JoonatanAlanampa/cartridge_pmod/rb.png

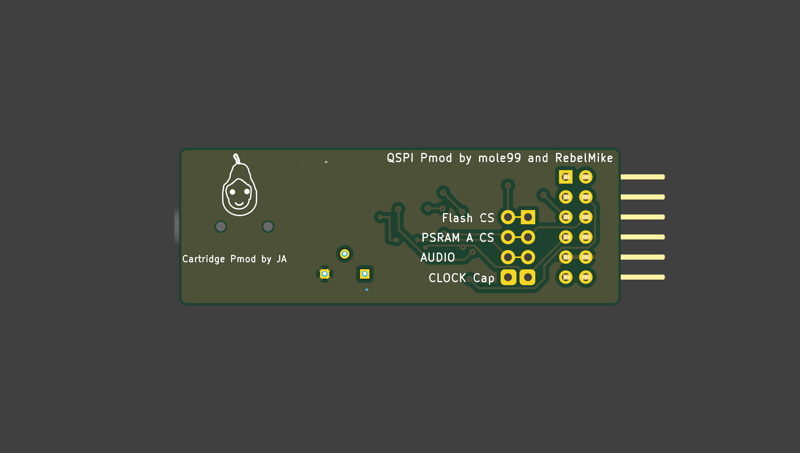
rb.png
