JoonatanAlanampa/cartridge_pmod/render_ext.png

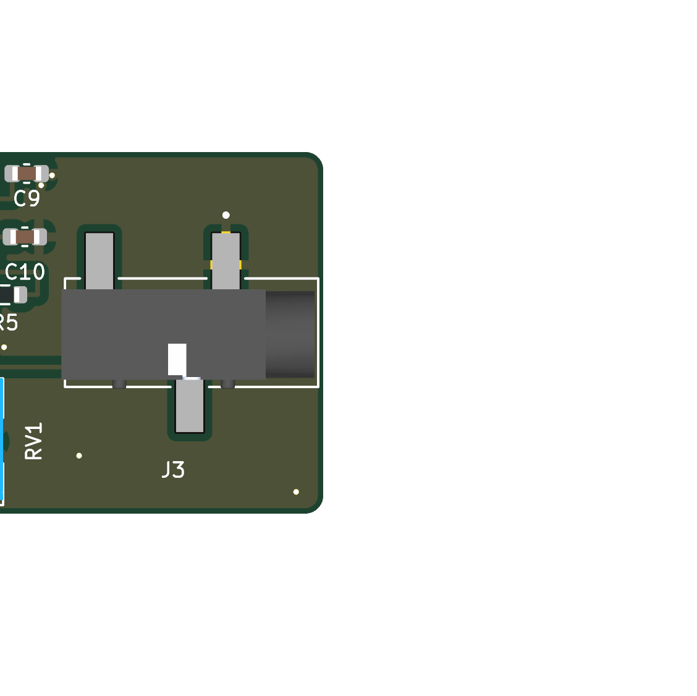
render_ext.png
