JoonatanAlanampa/cartridge_pmod/render_side_crop.png

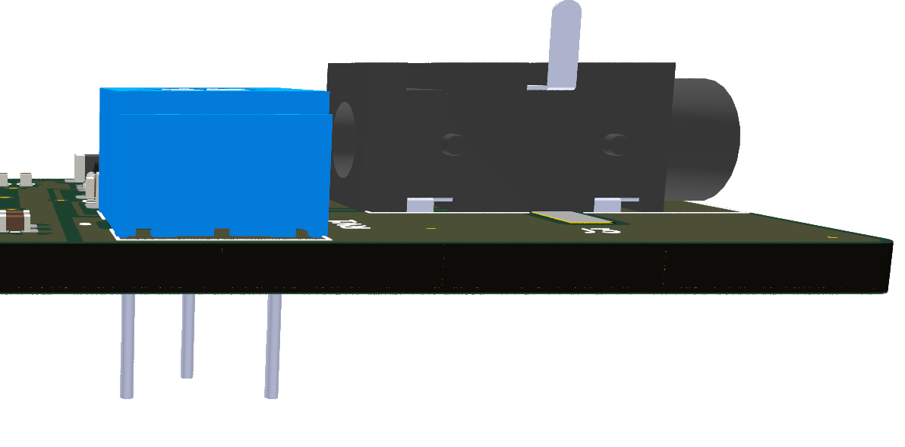
render_side_crop.png
