JoonatanAlanampa/cartridge_pmod/render_top.png

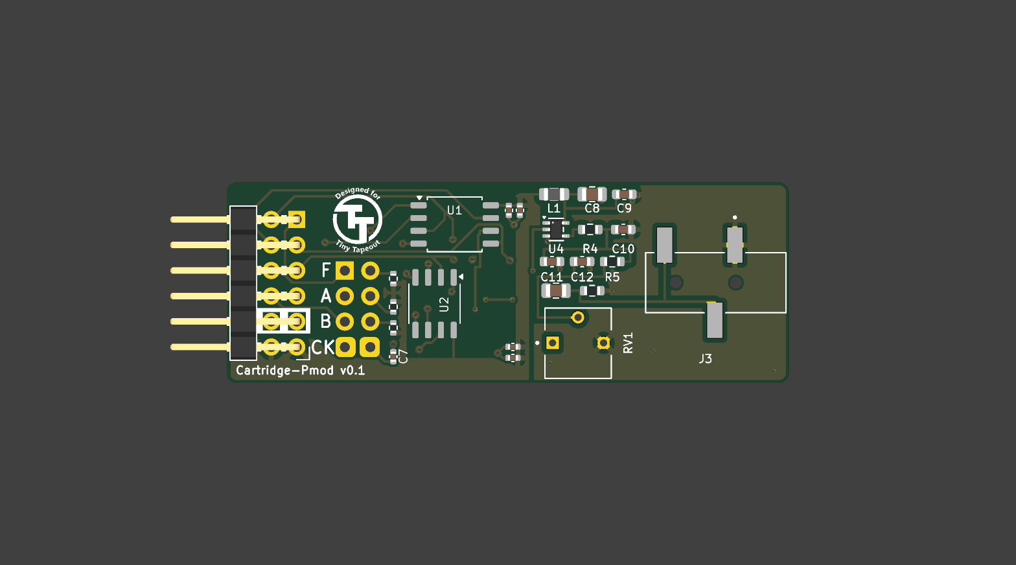
render_top.png
