JoonatanAlanampa/cartridge_pmod/rs_crop.png

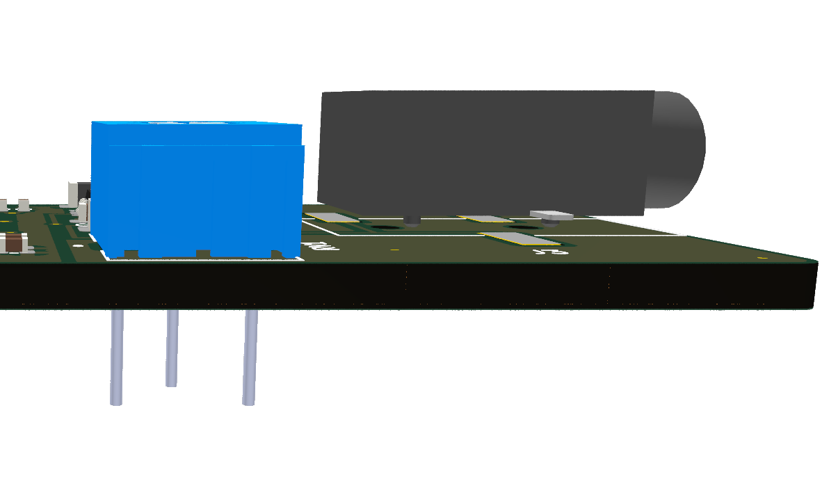
rs_crop.png
