JoonatanAlanampa/cartridge_pmod/rt_crop.png

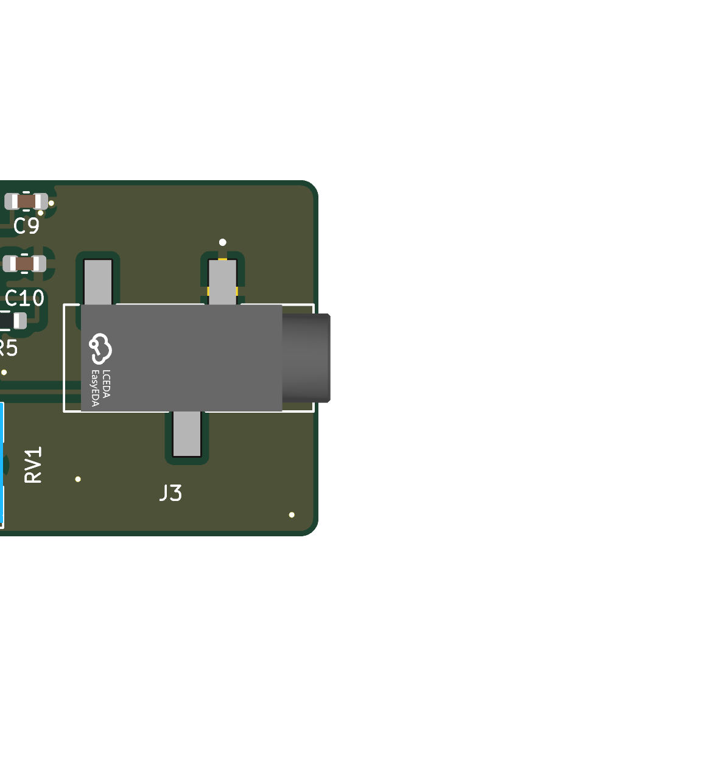
rt_crop.png
