JoonatanAlanampa/cartridge_pmod/tools/pearto_preview.png

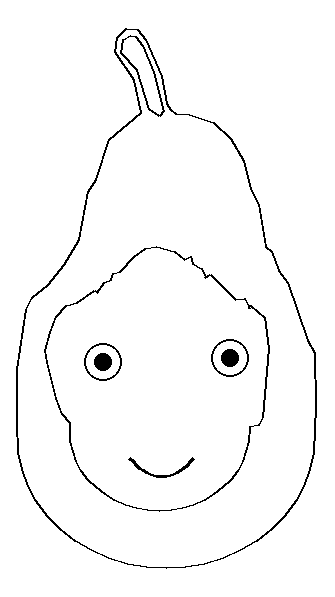
tools/pearto_preview.png
