JoonatanAlanampa/cartridge_pmod/refs/tt-audio-pmod/sim/ACSweep.asc

C1: cap; 100n
C2: cap; 47µ
C3: cap; 147n
R1: res; 33
R2: res; R={vol}
R3: res; 470
R4: res; 37R
R5: res; 17
R6: res; 120
V1: voltage; 1.6; AC 1.5 0
Named nets: out, 0
.param period=0.00001013/3
#.step param sweep list 0.001 0.0005 0.0002 0.0001 0.00005
.param sweep=0.001
.ac dec 20 1 1000000
#.step dec param vol 20 200 3
.param vol=180
