JoonatanAlanampa/cartridge_pmod/refs/tt-audio-pmod/sim/LineOutPWM.asc

B1: bv; V=3.3*((time/{period})-(int(time/{period}))<0.5+0.5*sin(2*pi*((time/{sweep})-(int(time/{sweep})))))
C1: cap; 100n
C2: cap; 47µ
C3: cap; 147n
R1: res; 33
R2: res; 33
R3: res; 470
R4: res; 37R
R5: res; 15k
R6: res; 120
Named nets: out, 0
.tran 0 0.205 0.2 0.00000005
.param period=0.00001013/3
.step param sweep list 0.01 0.003 0.001 0.0001 0.0000625
#.param sweep=0.01
