JoonatanAlanampa/cartridge_pmod/refs/tt-audio-pmod/sim/PowerSupply.asc

B1: bv; V=3.2+0.15*(0>sin(time/0.0000005))
B2: bv; V=120+10000*(0>sin(2*pi*time/0.000005))*(0>sin(2*pi*time/0.0001))
C1: cap; 10.1µ
L1: ind; 3.3µ; Ipk=50m Rser=0.6
R1: res; R=V(Vres)
Named nets: 0, Vres
.tran 0 0.003 0.001 0.00000001
